Lunardy2509/arduino_multimeter/documentation/IMG_5544.jpeg

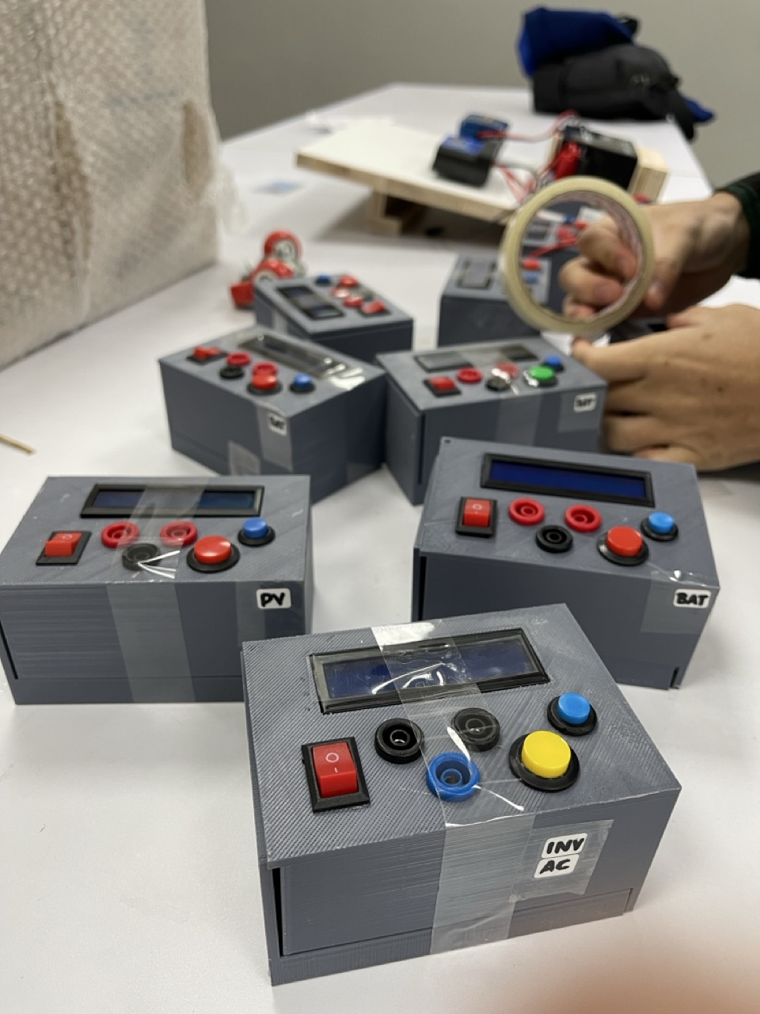
documentation/IMG_5544.jpeg
