Lunardy2509/arduino_multimeter/circuit schematics/PKM_MAN_IC_AC.kicad_sch

## KiCad design circuit schematics/PKM_MAN_IC_AC.kicad_sch (2024-04-24)

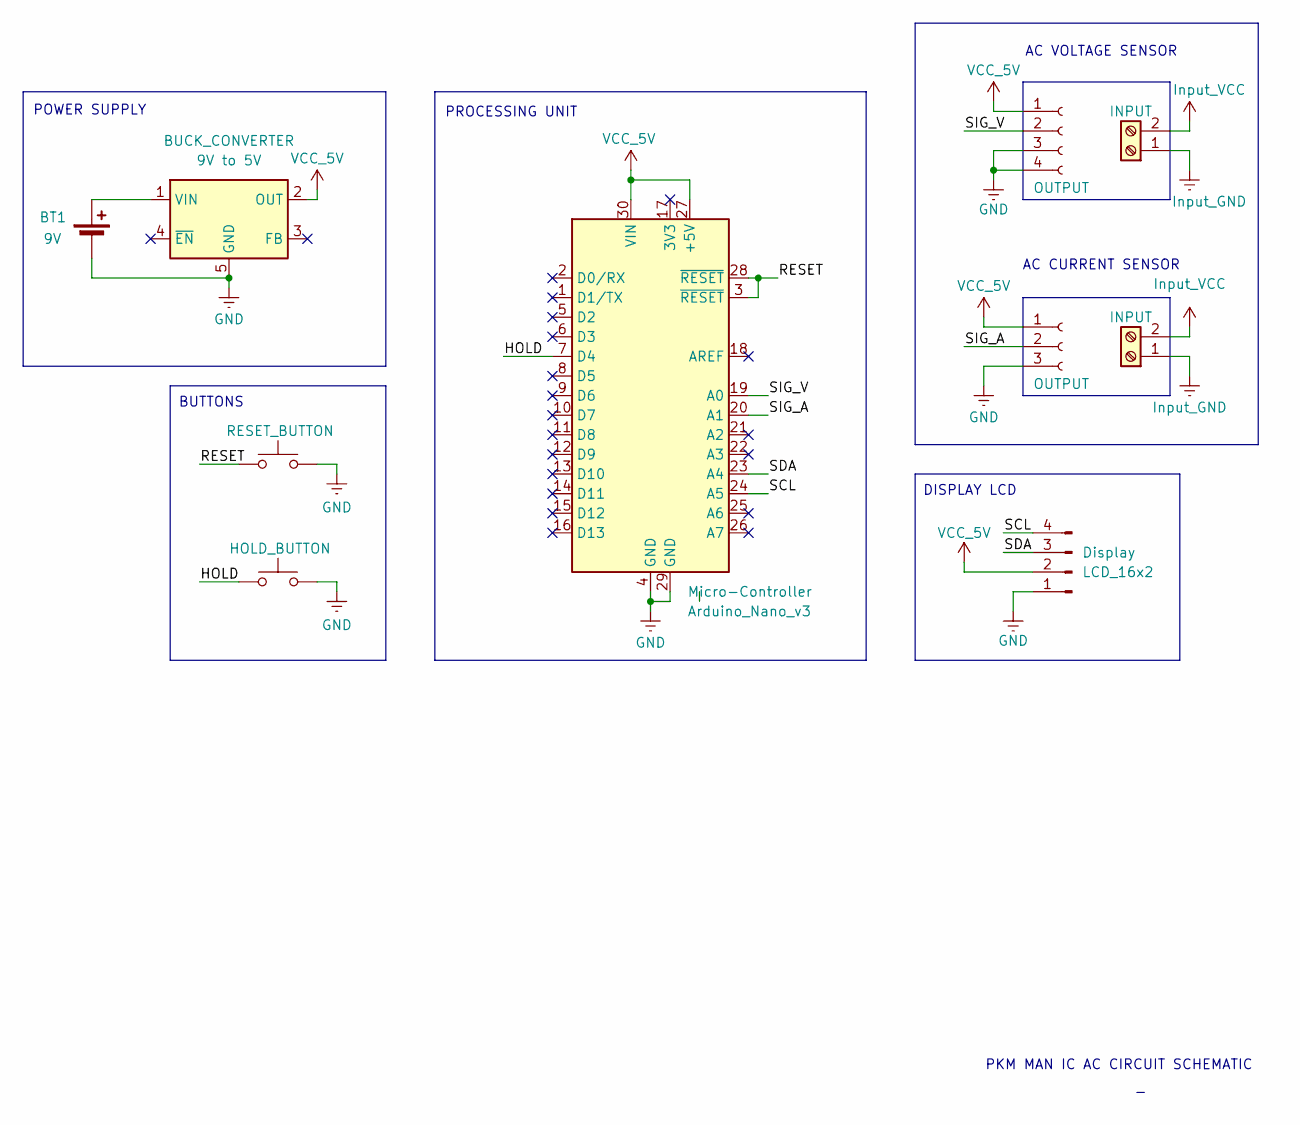
[picture p16: schematic PKM_MAN_IC_AC.kicad_sch]

Parts:
BT1: 9V
BUCK_CONVERTER: 9V to 5V; SOIC-8_3.9x4.9mm_P1.27mm
Display: LCD_16x2
HOLD_BUTTON: SW_Push
INPUT: Input_Vol
Micro-Controller: Arduino_Nano_v3; Arduino_Nano
OUTPUT: DC_Vol
RESET_BUTTON: SW_Push

Connections:
GND: BT1.2 (-), BUCK_CONVERTER.5 (GND), BUCK_CONVERTER.6 (GND), BUCK_CONVERTER.7 (GND), BUCK_CONVERTER.8 (GND), Display.1, HOLD_BUTTON.2, Micro-Controller.4 (GND), Micro-Controller.29 (GND), OUTPUT.3, OUTPUT.4, RESET_BUTTON.2
HOLD: HOLD_BUTTON.1, Micro-Controller.7 (D4)
Input_GND: INPUT.1
Input_VCC: INPUT.2
unnamed: BT1.1 (+), BUCK_CONVERTER.1 (VIN)
RESET: Micro-Controller.3 (~RESET), Micro-Controller.28 (~RESET), RESET_BUTTON.1
SCL: Display.4, Micro-Controller.24 (A5)
SDA: Display.3, Micro-Controller.23 (A4)
SIG_A: Micro-Controller.20 (A1), OUTPUT.2
SIG_V: Micro-Controller.19 (A0), OUTPUT.2
VCC_5V: BUCK_CONVERTER.2 (OUT), Display.2, Micro-Controller.27 (+5V), Micro-Controller.30 (VIN), OUTPUT.1

Notes on the sheet:
PKM MAN IC AC CIRCUIT SCHEMATIC
PROCESSING UNIT
AC CURRENT SENSOR
AC VOLTAGE SENSOR
BUTTONS
DISPLAY LCD
POWER SUPPLY
